anasluqman089/V-Power/Firmware/V-Power Firmware/mini_handheld_console/src/camera.cpp

#include "camera.h"
#include "storage.h"
#include <Arduino.h>
#include <FS.h>
#include <SD.h>
#include "esp_camera.h"

#define PWDN_GPIO_NUM -1
#define RESET_GPIO_NUM -1
#define XCLK_GPIO_NUM 10
#define SIOD_GPIO_NUM 40
#define SIOC_GPIO_NUM 39
#define Y9_GPIO_NUM 48
#define Y8_GPIO_NUM 11
#define Y7_GPIO_NUM 12
#define Y6_GPIO_NUM 14
#define Y5_GPIO_NUM 16
#define Y4_GPIO_NUM 18
#define Y3_GPIO_NUM 17
#define Y2_GPIO_NUM 15
#define VSYNC_GPIO_NUM 38
#define HREF_GPIO_NUM 47
#define PCLK_GPIO_NUM 13

static bool ready = false;

bool cameraBegin() {
    camera_config_t config = {};
    config.ledc_channel = LEDC_CHANNEL_0;
    config.ledc_timer = LEDC_TIMER_0;
    config.pin_d0 = Y2_GPIO_NUM;
    config.pin_d1 = Y3_GPIO_NUM;
    config.pin_d2 = Y4_GPIO_NUM;
    config.pin_d3 = Y5_GPIO_NUM;
    config.pin_d4 = Y6_GPIO_NUM;
    config.pin_d5 = Y7_GPIO_NUM;
    config.pin_d6 = Y8_GPIO_NUM;
    config.pin_d7 = Y9_GPIO_NUM;
    config.pin_xclk = XCLK_GPIO_NUM;
    config.pin_pclk = PCLK_GPIO_NUM;
    config.pin_vsync = VSYNC_GPIO_NUM;
    config.pin_href = HREF_GPIO_NUM;
    config.pin_sccb_sda = SIOD_GPIO_NUM;
    config.pin_sccb_scl = SIOC_GPIO_NUM;
    config.pin_pwdn = PWDN_GPIO_NUM;
    config.pin_reset = RESET_GPIO_NUM;
    config.xclk_freq_hz = 20000000;
    config.pixel_format = PIXFORMAT_JPEG;
    config.frame_size = FRAMESIZE_QQVGA;
    config.jpeg_quality = 12;
    config.fb_count = psramFound() ? 2 : 1;
    config.fb_location = psramFound() ? CAMERA_FB_IN_PSRAM : CAMERA_FB_IN_DRAM;
    ready = esp_camera_init(&config) == ESP_OK;
    return ready;
}

bool cameraReady() {
    return ready;
}

bool takePhoto() {
    if (!ready) return false;

    camera_fb_t *fb = esp_camera_fb_get();
    if (!fb) return false;

    String path = nextPhotoPath();
    File file = SD.open(path, FILE_WRITE);
    if (!file) {
        esp_camera_fb_return(fb);
        return false;
    }

    size_t length = fb->len;
    size_t written = file.write(fb->buf, length);
    file.close();
    esp_camera_fb_return(fb);

    if (written != length) return false;
    scanPhotos();
    return true;
}
