anasluqman089/V-Power/Firmware/V-Power Firmware/include/storage.h

#pragma once

#include <Arduino.h>
#include <vector>

extern std::vector<String> gameFiles;
extern std::vector<String> photoFiles;

bool storageBegin();
void scanGames();
void scanPhotos();
String nextPhotoPath();
